technotrasher/Weather-Stations-NIXIE/programm_esp/прошивка.jpg

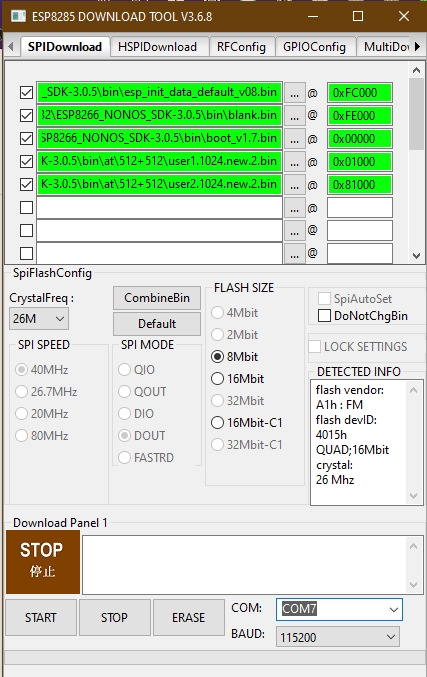
programm_esp/прошивка.jpg
