technotrasher/Weather-Stations-NIXIE/nixieClock_2_v3/BME.h

#define BMP180_ADDR 0x77  //адрес датчика

#define BMP180_CONTROL_REG 0xF4   //регистр настройки замеров
#define BMP180_DATA_OUT_REG 0xF6  //регистр чтения данных

#define BMP180_READ_TEMP 0x2E   //запрос температуры
#define BMP180_READ_PRESS 0x34  //запрос давления

#define BMP180_OVERSAMP 0x03  //разрешение датчика давления

#define BME280_ADDR 0x76  //адрес датчика

#define BME280_DATA_OUT_REG 0xF7      //регистр чтения данных
#define BME280_STATUS_REG 0xF3        //регистр статуса
#define BME280_CONFIG_REG 0xF5        //регистр основных настроек
#define BME280_CONTROL_HUM_REG 0xF2   //регистр настройки влажности
#define BME280_CONTROL_MEAS_REG 0xF4  //регистр настройки замеров

#define BME280_MODE 0x02         //режим замера по запросу
#define BME280_STANDBY 0x05      //замер каждую секунду
#define BME280_FILTER_COEF 0x04  //коэффициент фильтрации 16

#define BME280_PRESS_OVERSAMP 0x02  //разрешение датчика давления
#define BME280_TEMP_OVERSAMP 0x03   //разрешение датчика температуры
#define BME280_HUM_OVERSAMP 0x01    //разрешение датчика влажности

#define BME_CHECK_TIMEOUT 120  //таймаут ожидания(50..150)(мс)
static uint16_t effect_timer_bme;

//структура калибровок датчика BME280
struct CalibrationDataBME280 {
  uint16_t TEMP_1;
  int16_t TEMP_2;
  int16_t TEMP_3;
  uint16_t PRESS_1;
  int16_t PRESS_2;
  int16_t PRESS_3;
  int16_t PRESS_4;
  int16_t PRESS_5;
  int16_t PRESS_6;
  int16_t PRESS_7;
  int16_t PRESS_8;
  int16_t PRESS_9;
  uint8_t HUM_1;
  int16_t HUM_2;
  uint8_t HUM_3;
  int16_t HUM_4;
  int16_t HUM_5;
  int8_t HUM_6;
} CalibrationBME;

//структура калибровок датчика BMP180
struct CalibrationDataBMP180 {
  int16_t AC_1;
  int16_t AC_2;
  int16_t AC_3;
  uint16_t AC_4;
  uint16_t AC_5;
  uint16_t AC_6;
  int16_t B_1;
  int16_t B_2;
  int16_t MB;
  int16_t MC;
  int16_t MD;
} CalibrationBMP;

//--------------------------------------Запись одного байта------------------------------------------
void writeREG(uint8_t _addr, uint8_t _reg, uint8_t _data)  //Запись одного байта
{
  if (wireBeginTransmission(_addr)) return;  //начало передачи
  wireWrite(_reg);                           //устанавливаем адрес записи
  wireWrite(_data);                          //записываем байт
  wireEnd();                                 //конец передачи
}
//--------------------------------------Чтение калибровок датчика------------------------------------------
boolean readCalibrationBMP180(void)  //чтение калибровок датчика
{
  if (wireRequestFrom(BMP180_ADDR, 0xAA)) return 0;  //запрашиваем чтение данных, если нет ответа выходим

  CalibrationBMP.AC_1 = ((wireRead() << 8) | wireRead());  //читаем
  CalibrationBMP.AC_2 = ((wireRead() << 8) | wireRead());
  CalibrationBMP.AC_3 = ((wireRead() << 8) | wireRead());
  CalibrationBMP.AC_4 = ((wireRead() << 8) | wireRead());
  CalibrationBMP.AC_5 = ((wireRead() << 8) | wireRead());
  CalibrationBMP.AC_6 = ((wireRead() << 8) | wireRead());
  CalibrationBMP.B_1 = ((wireRead() << 8) | wireRead());
  CalibrationBMP.B_2 = ((wireRead() << 8) | wireRead());
  CalibrationBMP.MB = ((wireRead() << 8) | wireRead());
  CalibrationBMP.MC = ((wireRead() << 8) | wireRead());
  CalibrationBMP.MD = ((wireRead() << 8) | wireReadEndByte());

  return 1;
}
//--------------------------------------Чтение калибровок датчика------------------------------------------
boolean readCalibrationBME280(void)  //чтение калибровок датчика
{
  if (wireRequestFrom(BME280_ADDR, 0x88)) return 0;  //запрашиваем чтение данных, если нет ответа выходим

  CalibrationBME.TEMP_1 = (wireRead() | (wireRead() << 8));  //читаем
  CalibrationBME.TEMP_2 = (wireRead() | (wireRead() << 8));
  CalibrationBME.TEMP_3 = (wireRead() | (wireRead() << 8));
  CalibrationBME.PRESS_1 = (wireRead() | (wireRead() << 8));
  CalibrationBME.PRESS_2 = (wireRead() | (wireRead() << 8));
  CalibrationBME.PRESS_3 = (wireRead() | (wireRead() << 8));
  CalibrationBME.PRESS_4 = (wireRead() | (wireRead() << 8));
  CalibrationBME.PRESS_5 = (wireRead() | (wireRead() << 8));
  CalibrationBME.PRESS_6 = (wireRead() | (wireRead() << 8));
  CalibrationBME.PRESS_7 = (wireRead() | (wireRead() << 8));
  CalibrationBME.PRESS_8 = (wireRead() | (wireRead() << 8));
  CalibrationBME.PRESS_9 = (wireRead() | (wireRead() << 8));
  CalibrationBME.HUM_1 = wireReadEndByte();

  if (wireRequestFrom(BME280_ADDR, 0xE1)) return 0;  //запрашиваем чтение данных, если нет ответа выходим

  CalibrationBME.HUM_2 = (wireRead() | (wireRead() << 8));  //читаем
  CalibrationBME.HUM_3 = wireRead();
  CalibrationBME.HUM_4 = (wireRead() << 4);
  uint8_t interVal = wireRead();
  CalibrationBME.HUM_4 |= (interVal & 0x0F);
  CalibrationBME.HUM_5 = (((interVal & 0xF0) >> 4) | (wireRead() << 4));
  CalibrationBME.HUM_6 = wireReadEndByte();

  return 1;
}
//--------------------------------------Чтение температуры/давления/влажности------------------------------------------
void readTempBME(void)  //чтение температуры/давления/влажности
{
  static uint8_t typeBME;  //тип датчика BME

  if (!typeBME) {  //если датчик не определен
    if (readCalibrationBMP180()) typeBME = BMP180_ADDR;
    else if (readCalibrationBME280()) {
      typeBME = BME280_ADDR;
      writeREG(BME280_ADDR, BME280_CONTROL_HUM_REG, BME280_HUM_OVERSAMP);                                                          //устанавливаем разрешение датчика влажности
      writeREG(BME280_ADDR, BME280_CONTROL_MEAS_REG, ((BME280_TEMP_OVERSAMP << 5) | (BME280_PRESS_OVERSAMP << 2) | BME280_MODE));  //устанавливаем разрешение датчика температуры и датчика давления, устанавливаем режим работы
      writeREG(BME280_ADDR, BME280_CONFIG_REG, ((BME280_STANDBY << 5) | (BME280_FILTER_COEF << 2)));                               //устанавливаем частоту опроса и коэффициент фильтрации
    } else return;                                                                                                                 //иначе выходим
  }

  switch (typeBME) {  //чтение данных
    case BMP180_ADDR:
      {
        int32_t temp_raw;   //регистр температуры
        int32_t press_raw;  //регистр давления

        writeREG(BMP180_ADDR, BMP180_CONTROL_REG, BMP180_READ_TEMP);  //запустили замер температуры
        effect_timer_bme = millis();
        while (1) {                                                      //ожидаем окончания замера
          if (wireRequestFrom(BMP180_ADDR, BMP180_CONTROL_REG)) return;  //запрашиваем чтение данных, если нет ответа выходим
          if (!(wireReadEndByte() & 0x20)) break;                        //если замер завершён продолжаем
          if (millis() - effect_timer_bme > BME_CHECK_TIMEOUT) return;   //выходим если таймаут
        }

        if (wireRequestFrom(BMP180_ADDR, BMP180_DATA_OUT_REG)) return;  //запрашиваем чтение данных, если нет ответа выходим
        temp_raw = (((uint16_t)wireRead() << 8) | wireReadEndByte());

        writeREG(BMP180_ADDR, BMP180_CONTROL_REG, BMP180_READ_PRESS | (BMP180_OVERSAMP << 6));  //запустили замер давления
        effect_timer_bme = millis();
        while (1) {                                                      //ожидаем окончания замера
          if (wireRequestFrom(BMP180_ADDR, BMP180_CONTROL_REG)) return;  //запрашиваем чтение данных, если нет ответа выходим
          if (!(wireReadEndByte() & 0x20)) break;                        //если замер завершён продолжаем
          if (millis() - effect_timer_bme > BME_CHECK_TIMEOUT) return;   //выходим если таймаут
        }

        if (wireRequestFrom(BMP180_ADDR, BMP180_DATA_OUT_REG)) return;  //запрашиваем чтение данных, если нет ответа выходим
        press_raw = (((uint32_t)wireRead() << 16) | ((uint32_t)wireRead() << 8) | wireReadEndByte());
        press_raw >>= (8 - BMP180_OVERSAMP);

        int32_t temp_val_1 = ((temp_raw - CalibrationBMP.AC_6) * CalibrationBMP.AC_5 >> 15) + ((int32_t)CalibrationBMP.MC << 11) / (((temp_raw - CalibrationBMP.AC_6) * CalibrationBMP.AC_5 >> 15) + CalibrationBMP.MD);
        uint32_t press_val_1 = ((uint32_t)CalibrationBMP.AC_4 * (uint32_t)(((((CalibrationBMP.AC_3 * (temp_val_1 - 4000)) >> 13) + ((CalibrationBMP.B_1 * (((temp_val_1 - 4000) * (temp_val_1 - 4000)) >> 12)) >> 16) + 2) >> 2) + 32768)) >> 15;
        uint32_t press_val_2 = ((uint32_t)press_raw - ((((CalibrationBMP.AC_1 * 4 + ((CalibrationBMP.B_2 * (((temp_val_1 - 4000) * (temp_val_1 - 4000)) >> 12)) >> 11) + ((CalibrationBMP.AC_2 * (temp_val_1 - 4000)) >> 11)) << BMP180_OVERSAMP) + 2) >> 2)) * (uint32_t)(50000UL >> BMP180_OVERSAMP);
        int32_t press_val_3 = (press_val_2 < 0x80000000) ? (press_val_2 * 2 / press_val_1) : (press_val_2 / press_val_1 * 2);

        uint16_t temp = ((temp_val_1 + 8) >> 4) * 10;                                                                                                               //записываем знаковую температуру в беззнаковую переменную
        tempSens.temp = (temp > 8500) ? 0 : temp;                                                                                                                       //установили температуру
        tempSens.press = (float)(press_val_3 + (((((press_val_3 >> 8) * (press_val_3 >> 8) * 3038) >> 16) + ((-7357 * press_val_3) >> 16) + 3791) >> 4)) * 0.00750062;  //записываем давление в мм рт.ст.
        tempSens.hum = 0;                                                                                                                                               //сбросили влажность
      }
      break;

    case BME280_ADDR:
      {
        writeREG(BME280_ADDR, BME280_CONTROL_MEAS_REG, ((BME280_TEMP_OVERSAMP << 5) | (BME280_PRESS_OVERSAMP << 2) | BME280_MODE));  //устанавливаем разрешение датчика температуры и датчика давления, устанавливаем режим работы
        effect_timer_bme = millis();
        while (1) {                                                     //ожидаем окончания замера
          if (wireRequestFrom(BME280_ADDR, BME280_STATUS_REG)) return;  //запрашиваем чтение данных, если нет ответа выходим
          if (!(wireReadEndByte() & 0x08)) break;                       //если замер завершён продолжаем
          if (millis() - effect_timer_bme > BME_CHECK_TIMEOUT) return;  //выходим если таймаут
        }
        if (wireRequestFrom(BME280_ADDR, BME280_DATA_OUT_REG)) return;  //запрашиваем чтение данных, если нет ответа выходим

        uint32_t press_raw = (((uint32_t)wireRead() << 16) | ((uint32_t)wireRead() << 8) | (uint32_t)wireRead()) >> 4;  //читаем 24-х битное значение ацп давления
        int32_t temp_raw = (((uint32_t)wireRead() << 16) | ((uint32_t)wireRead() << 8) | (uint32_t)wireRead()) >> 4;    //читаем 24-х битное значение ацп температуры
        int32_t hum_raw = ((uint16_t)wireRead() << 8) | (uint16_t)wireReadEndByte();                                    //читаем 16-и битное значение ацп влажности


        int32_t temp_val_1 = ((((temp_raw >> 3) - ((int32_t)CalibrationBME.TEMP_1 << 1))) * ((int32_t)CalibrationBME.TEMP_2)) >> 11;
        int32_t temp_val_2 = (((((temp_raw >> 4) - ((int32_t)CalibrationBME.TEMP_1)) * ((temp_raw >> 4) - ((int32_t)CalibrationBME.TEMP_1))) >> 12) * ((int32_t)CalibrationBME.TEMP_3)) >> 14;
        temp_raw = temp_val_1 + temp_val_2;         //цельночисленная температура
        uint16_t temp = (temp_raw * 5 + 128) >> 8;  //записываем знаковую температуру в беззнаковую переменную
        tempSens.temp = (temp > 8500) ? 0 : temp;       //установили температуру


        int64_t press_val_1 = ((int64_t)temp_raw) - 128000;  //компенсация температуры
        int64_t press_val_2 = press_val_1 * press_val_1 * (int64_t)CalibrationBME.PRESS_6;
        press_val_2 = press_val_2 + ((press_val_1 * (int64_t)CalibrationBME.PRESS_5) << 17);
        press_val_2 = press_val_2 + (((int64_t)CalibrationBME.PRESS_4) << 35);
        press_val_1 = ((press_val_1 * press_val_1 * (int64_t)CalibrationBME.PRESS_3) >> 8) + ((press_val_1 * (int64_t)CalibrationBME.PRESS_2) << 12);
        press_val_1 = (((((int64_t)1) << 47) + press_val_1)) * ((int64_t)CalibrationBME.PRESS_1) >> 33;
        if (press_val_1) {  //если значение не нулевое
          int64_t press_val_3 = 1048576 - press_raw;
          press_val_3 = (((press_val_3 << 31) - press_val_2) * 3125) / press_val_1;
          press_val_1 = (((int64_t)CalibrationBME.PRESS_9) * (press_val_3 >> 13) * (press_val_3 >> 13)) >> 25;
          press_val_2 = (((int64_t)CalibrationBME.PRESS_8) * press_val_3) >> 19;
          press_val_3 = ((press_val_3 + press_val_1 + press_val_2) >> 8) + (((int64_t)CalibrationBME.PRESS_7) << 4);

          tempSens.press = ((float)press_val_3 / 256.0) * 0.00750062;  //записываем давление в мм рт.ст.
        } else tempSens.press = 0;                                     //иначе записываем 0


        int32_t hum_val = (temp_raw - ((int32_t)76800));  //компенсация температуры
        hum_val = (((((hum_raw << 14) - (((int32_t)CalibrationBME.HUM_4) << 20) - (((int32_t)CalibrationBME.HUM_5) * hum_val)) + ((int32_t)16384)) >> 15) * (((((((hum_val * ((int32_t)CalibrationBME.HUM_6)) >> 10) * (((hum_val * ((int32_t)CalibrationBME.HUM_3)) >> 11) + ((int32_t)32768))) >> 10) + ((int32_t)2097152)) * ((int32_t)CalibrationBME.HUM_2) + 8192) >> 14));
        hum_val = (hum_val - (((((hum_val >> 15) * (hum_val >> 15)) >> 7) * ((int32_t)CalibrationBME.HUM_1)) >> 4));
        hum_val = (hum_val < 0) ? 0 : hum_val;
        hum_val = (hum_val > 419430400) ? 419430400 : hum_val;

        tempSens.hum = (hum_val >> 12) / 1024.0;  //записываем влажность в %
      }
      break;
  }
  tempSens.err = 0;  //сбросили ошибку датчика температуры
}
